boricha/HP6060B/schematic/bottom.png

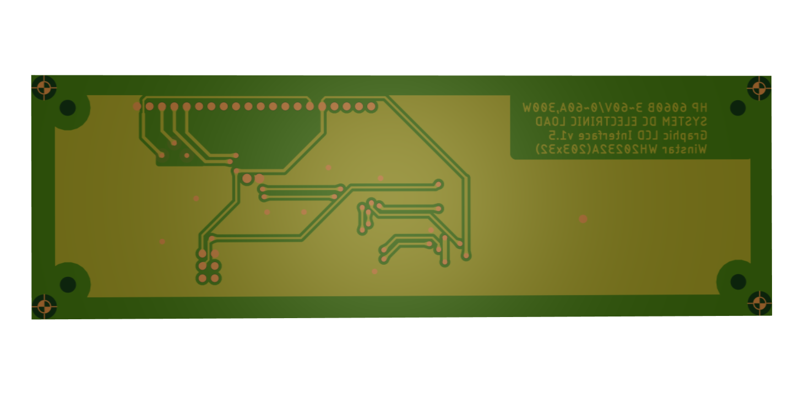
schematic/bottom.png
